noredlace/TheOrgoNaut/orgonaut66/IMG_20180920_210546.jpg

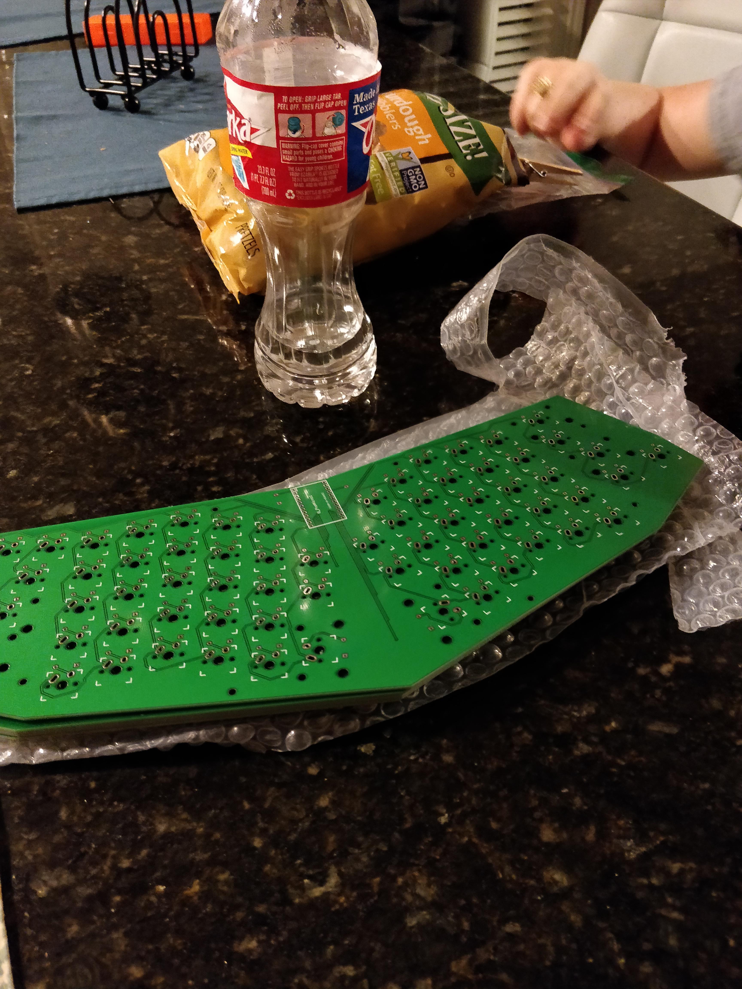
orgonaut66/IMG_20180920_210546.jpg
