noredlace/TheOrgoNaut/pics/orgonaut66 back pcb.png

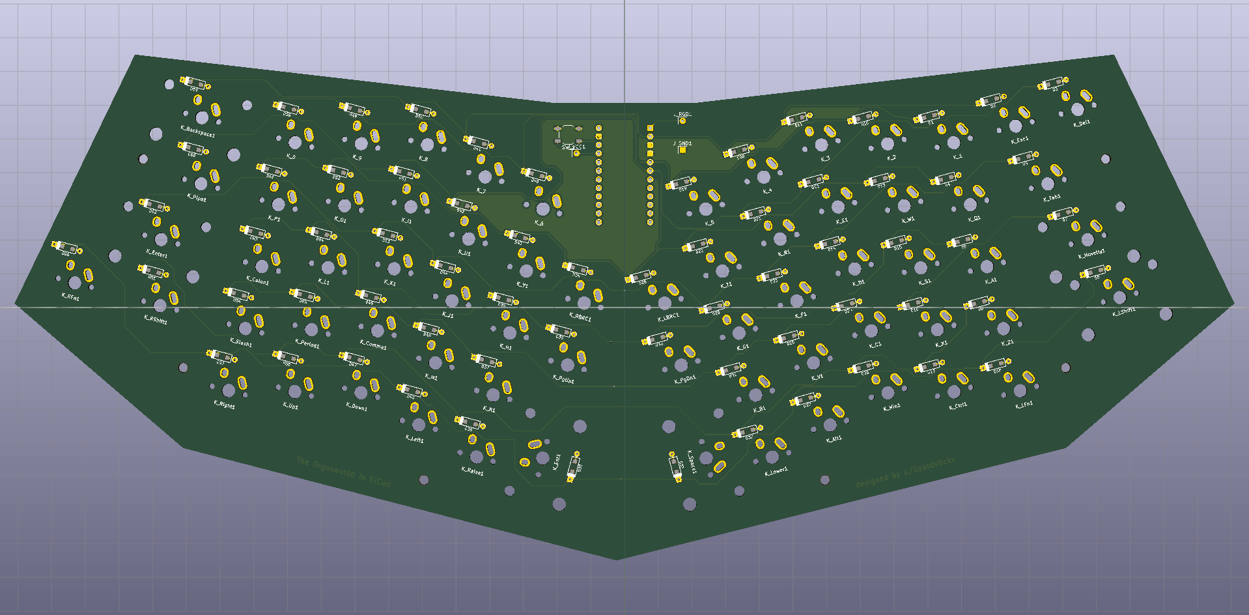
pics/orgonaut66 back pcb.png
