noredlace/TheOrgoNaut/pics/orgonaut66 front pcb v2.png

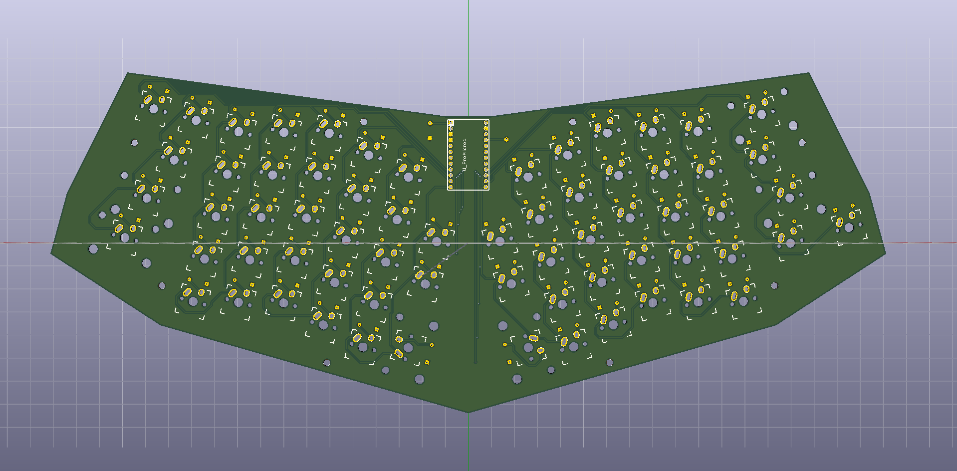
pics/orgonaut66 front pcb v2.png
