noredlace/TheOrgoNaut/pics/orgonaut66 front pcb.png

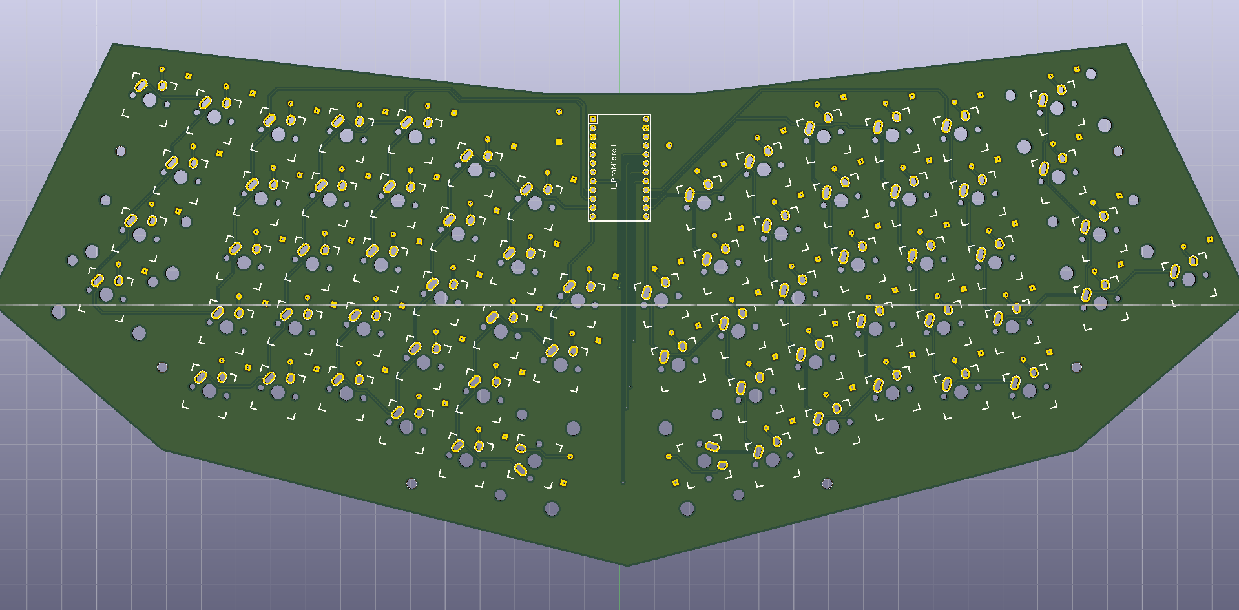
pics/orgonaut66 front pcb.png
